jyojoh/case-designs/corne/6-column Choc/Integrated/leftIntegratedBottomSix.step

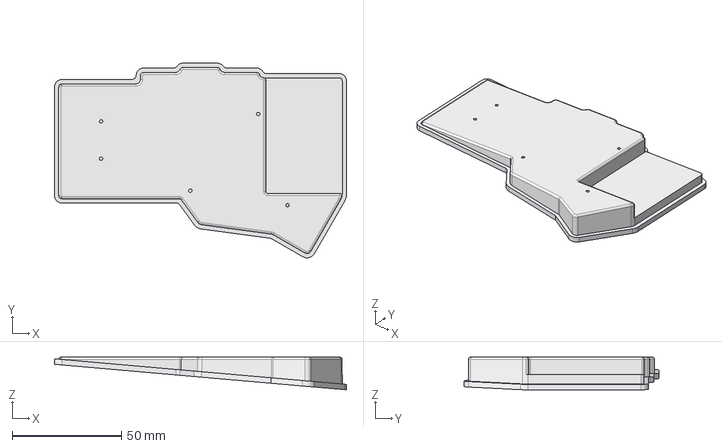
[picture p14: CAD file, 2023-08-03]
corne/6-column Choc/Integrated/leftIntegratedBottomSix.step
133.7 x 89.2 x 15.0 mm
