jyojoh/case-designs/corne/buttonSliderSlim.stl

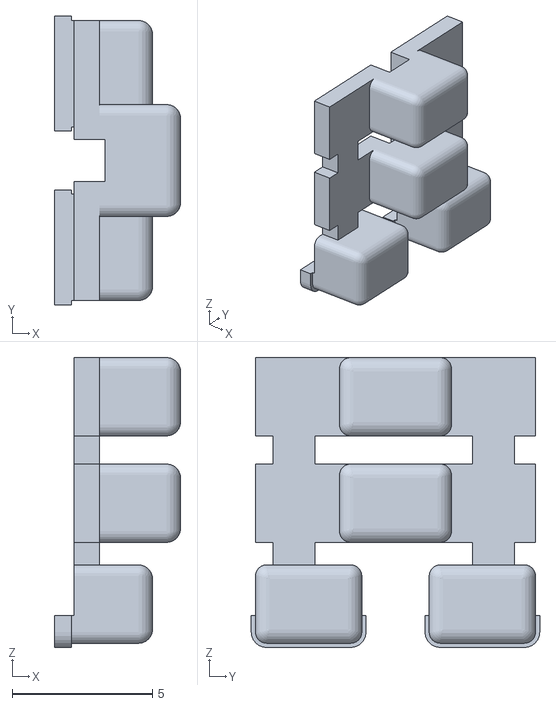
[picture p15: CAD file, 2023-08-01]
corne/buttonSliderSlim.stl
4.50 x 10.3 x 10.3
