jyojoh/case-designs/corne/5-column Choc/Integrated/rightIntegrated.step

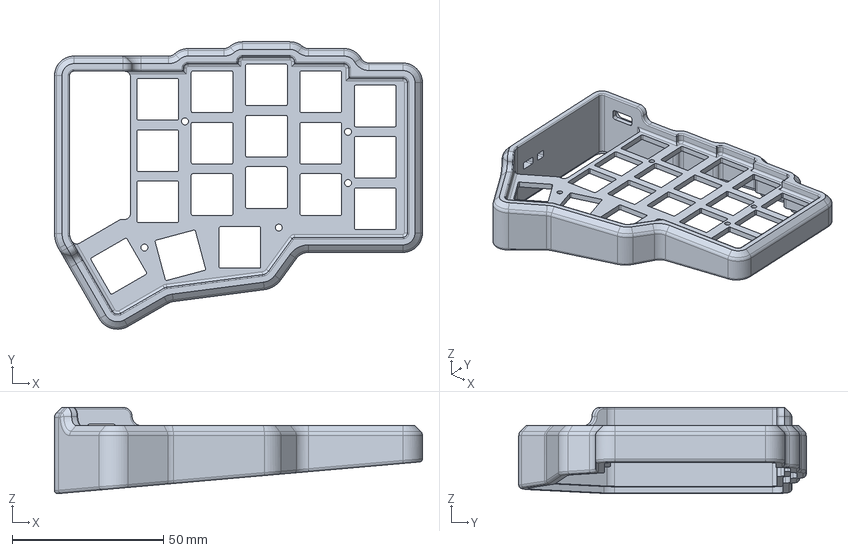
[picture p16: CAD file, 2023-07-31]
corne/5-column Choc/Integrated/rightIntegrated.step
121.8 x 95.2 x 28.6 mm
