jyojoh/case-designs/corne/buttonSlider.stl

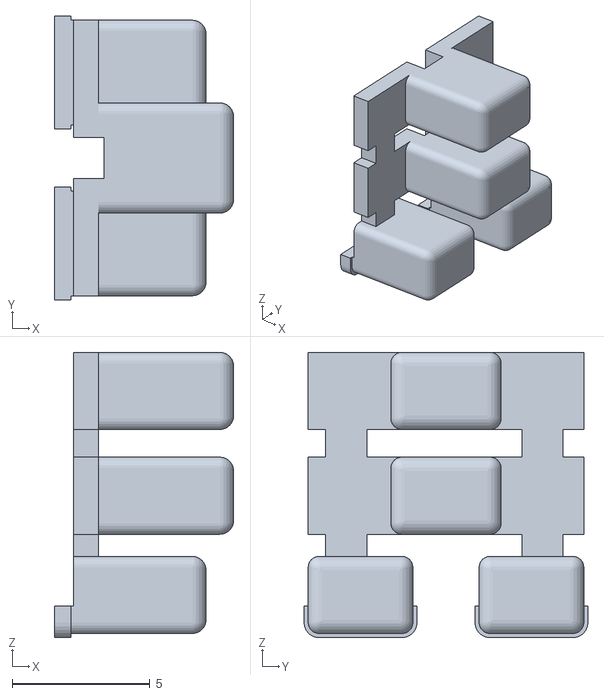
[picture p17: CAD file, 2023-07-31]
corne/buttonSlider.stl
6.50 x 10.3 x 10.3
